darthcloud/cube64-dx/notes/analyzer/rd1_s1.png

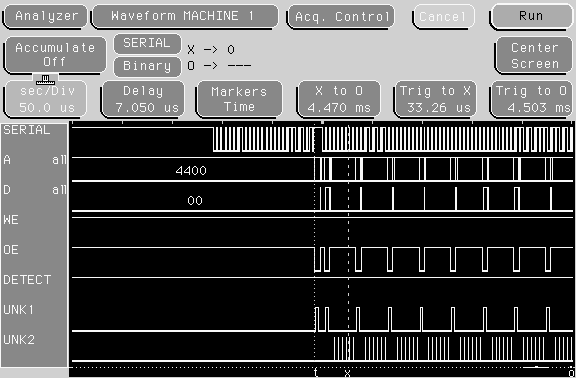
notes/analyzer/rd1_s1.png
