darthcloud/cube64-dx/notes/analyzer/rd1_s2.png

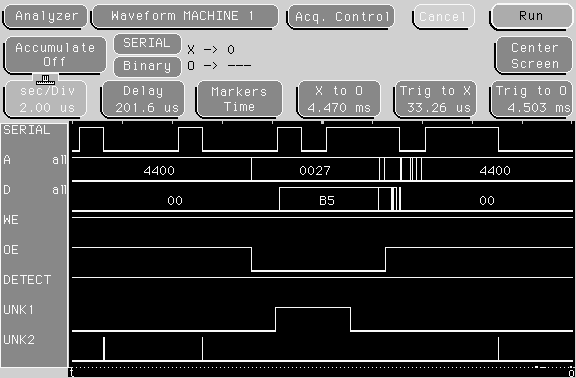
notes/analyzer/rd1_s2.png
