darthcloud/cube64-dx/notes/analyzer/wr1_s1.png

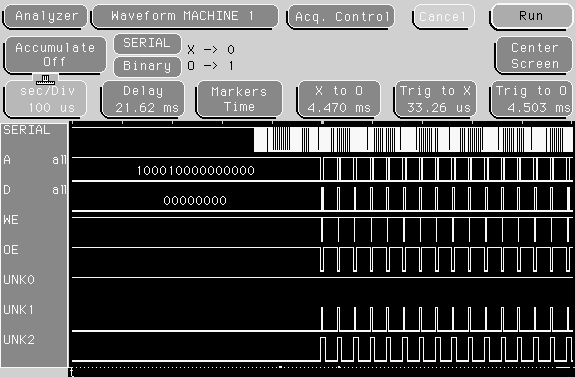
notes/analyzer/wr1_s1.png
